erdemcanaz/EE313-Term-project/Pictures/Control Unit/control unit4.png

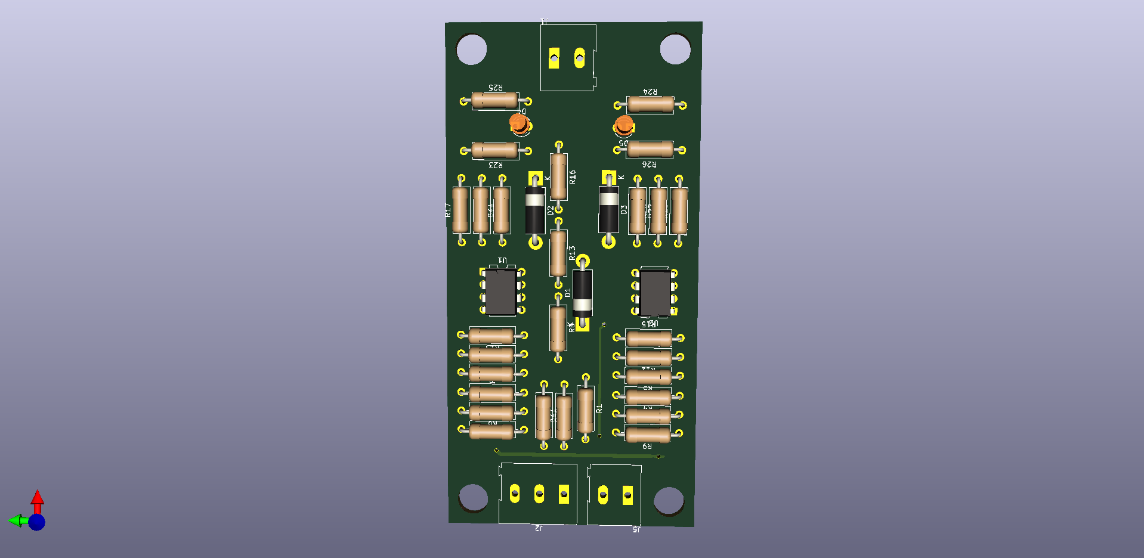
Pictures/Control Unit/control unit4.png
