erdemcanaz/EE313-Term-project/Pictures/Control Unit/ltspice simulation of fan noisy.png

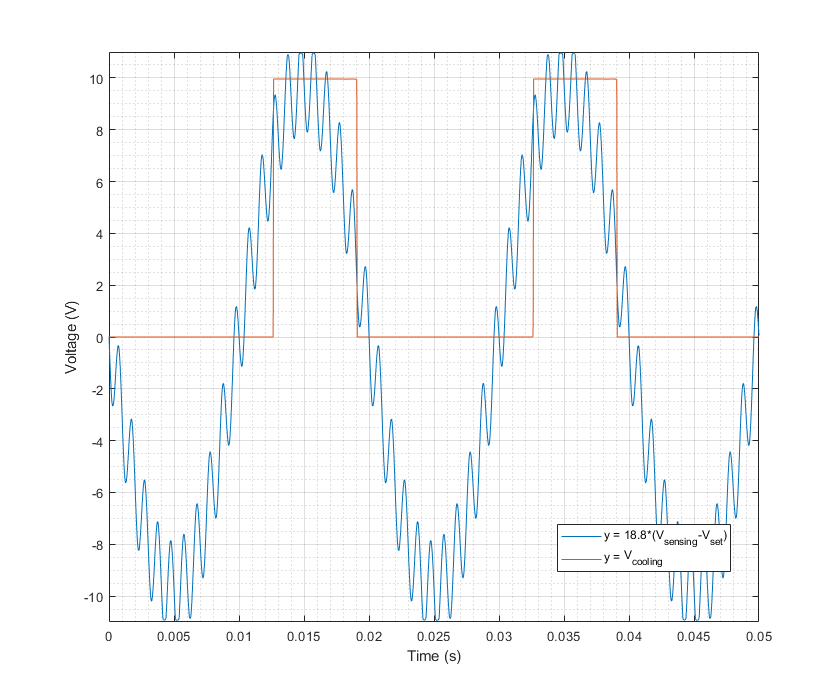
Pictures/Control Unit/ltspice simulation of fan noisy.png
