erdemcanaz/EE313-Term-project/Pictures/Control Unit/ltspice simulation of fan wandwo noise.png

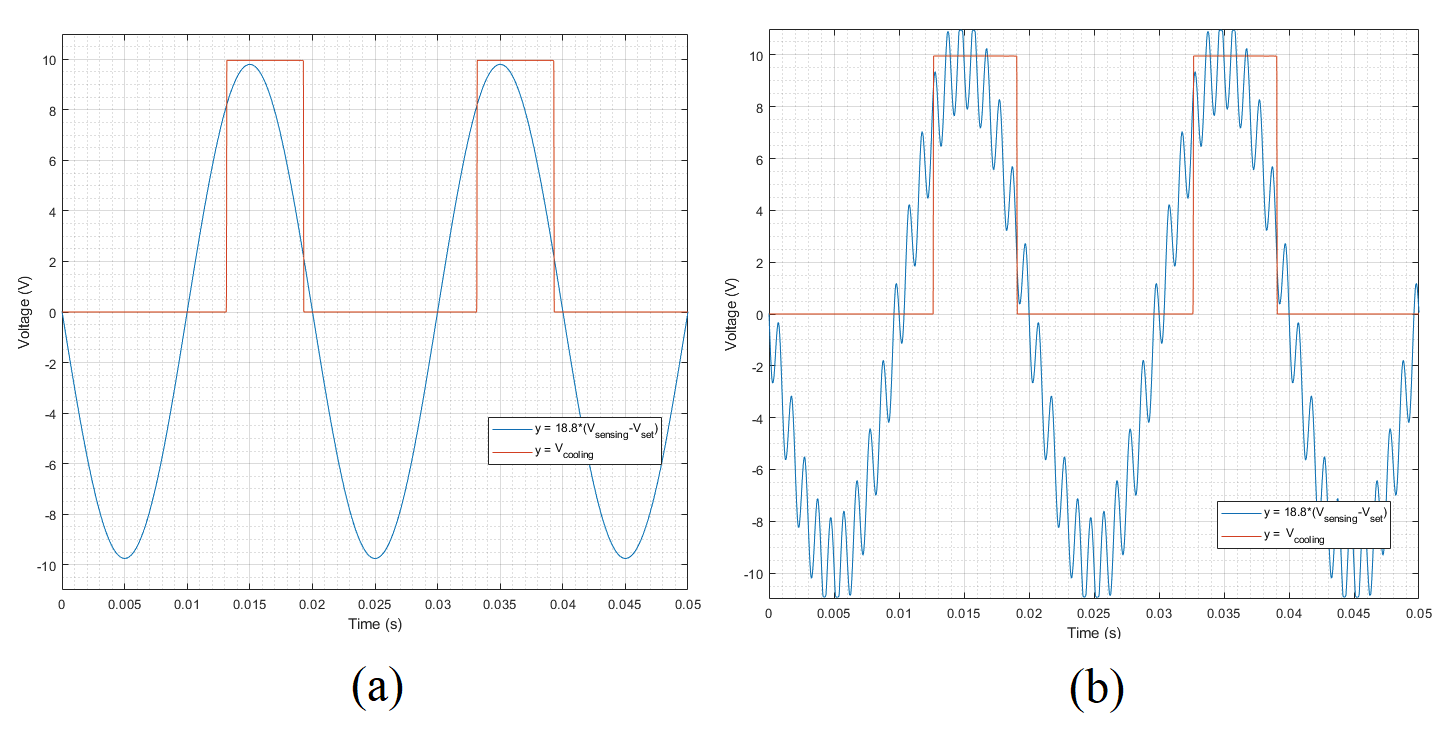
Pictures/Control Unit/ltspice simulation of fan wandwo noise.png
