erdemcanaz/EE313-Term-project/Pictures/Control Unit/ltspice simulation of fan.png

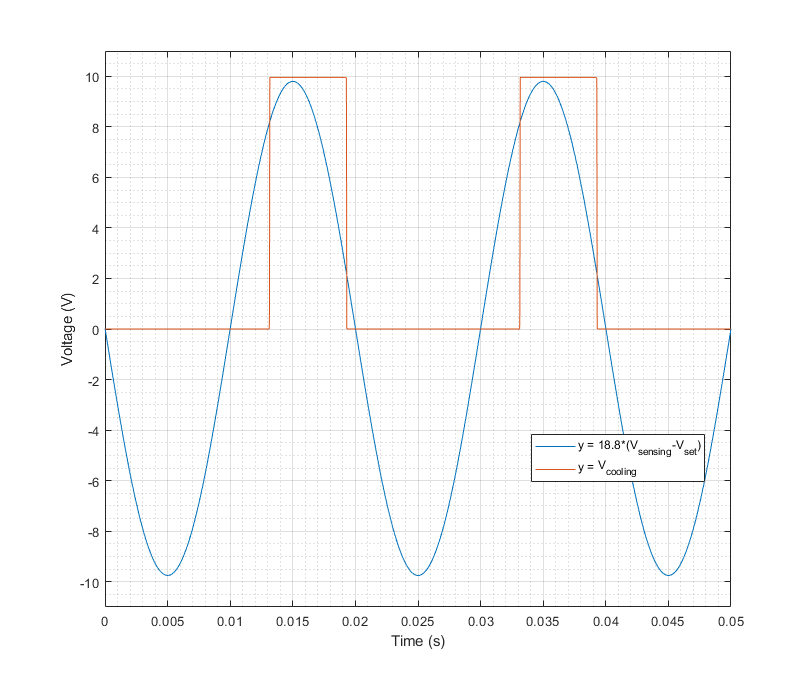
Pictures/Control Unit/ltspice simulation of fan.png
