erdemcanaz/EE313-Term-project/Pictures/Control Unit/schmitt trigger circuit.png

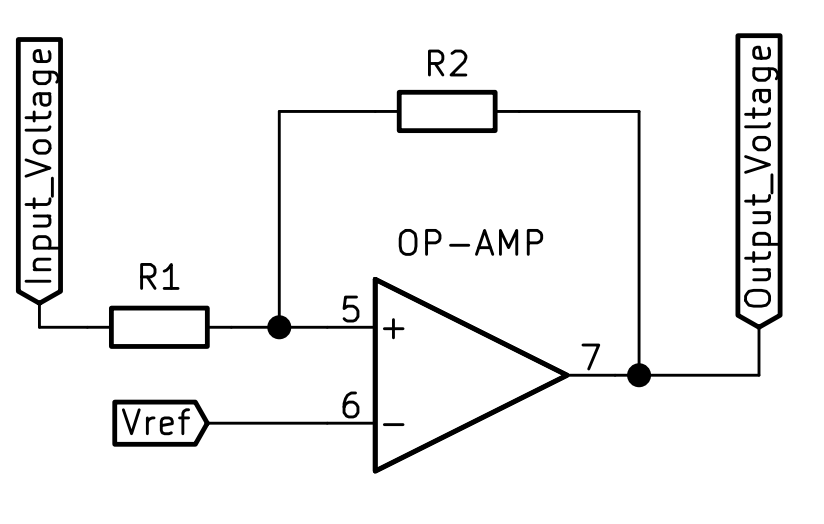
Pictures/Control Unit/schmitt trigger circuit.png
