erdemcanaz/EE313-Term-project/Pictures/display unit/simulationresults.png

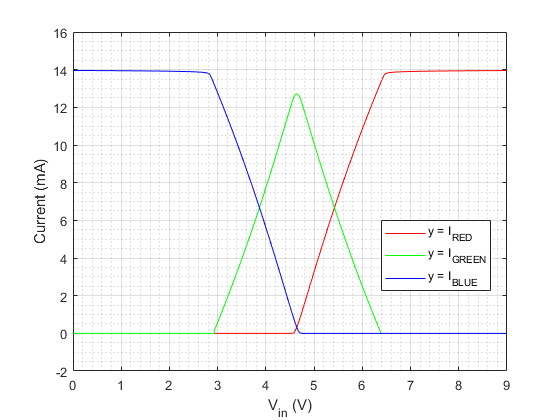
Pictures/display unit/simulationresults.png
