erdemcanaz/EE313-Term-project/Pictures/Sensing Unit/amplified signal.png

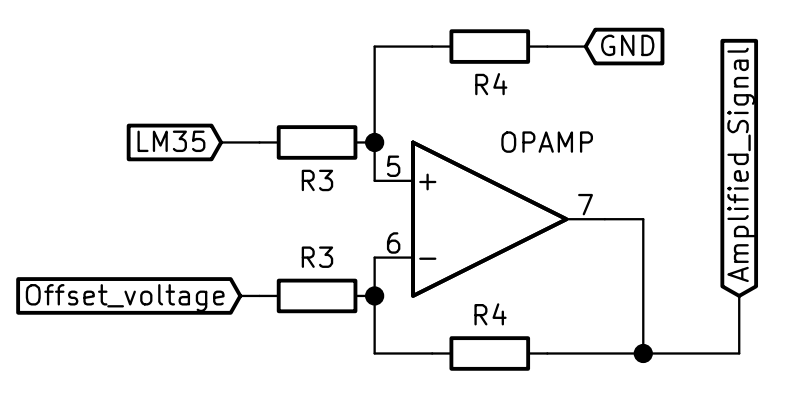
Pictures/Sensing Unit/amplified signal.png
