erdemcanaz/EE313-Term-project/Pictures/Sensing Unit/offset_voltage.png

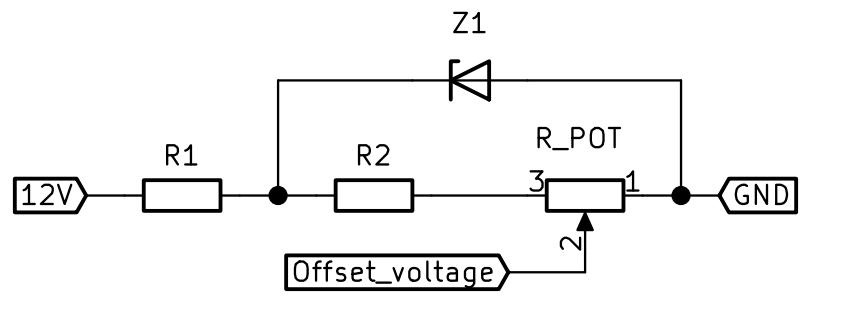
Pictures/Sensing Unit/offset_voltage.png
