erdemcanaz/EE313-Term-project/Pictures/Sensing Unit/osciloscope.png

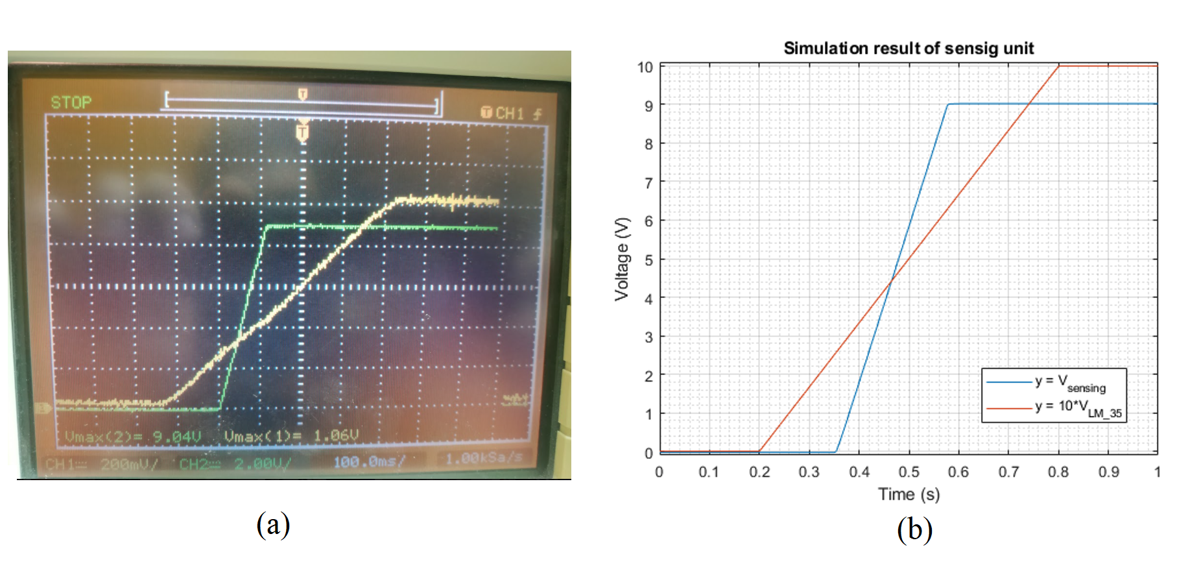
Pictures/Sensing Unit/osciloscope.png
