erdemcanaz/EE313-Term-project/Pictures/Sensing Unit/power connection indicators.png

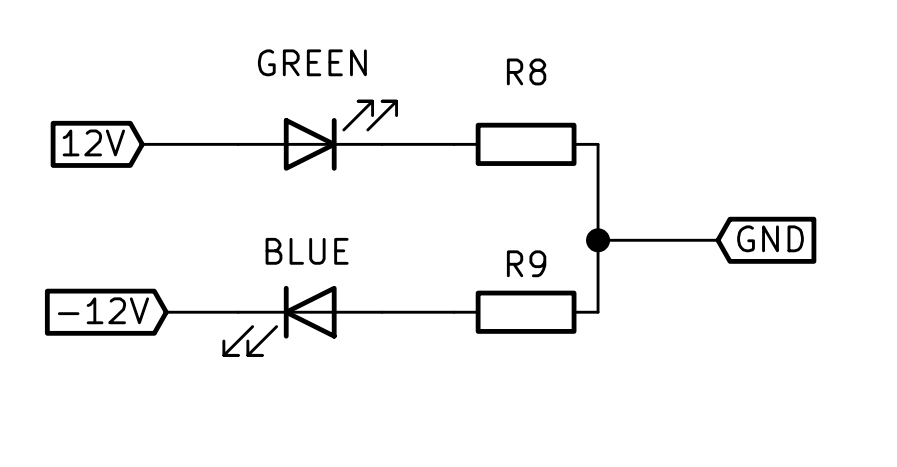
Pictures/Sensing Unit/power connection indicators.png
