erdemcanaz/EE313-Term-project/Simulation/Control Unit - 4/0.2C-0.1mV noise with 1khz on top of 1C temp difference.png

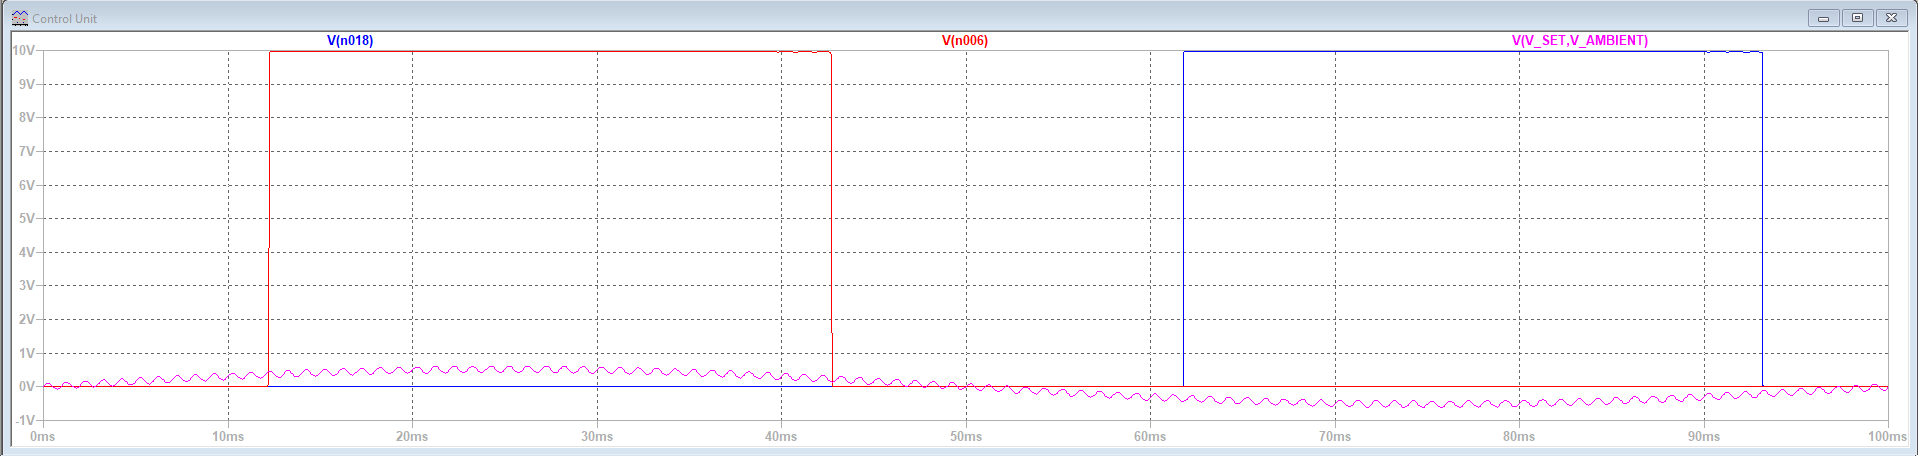
Simulation/Control Unit - 4/0.2C-0.1mV noise with 1khz on top of 1C temp difference.png
