erdemcanaz/EE313-Term-project/Simulation/Control Unit - 4/1C-0.53mV noise with 1khz on top of 1C temperature difference.png

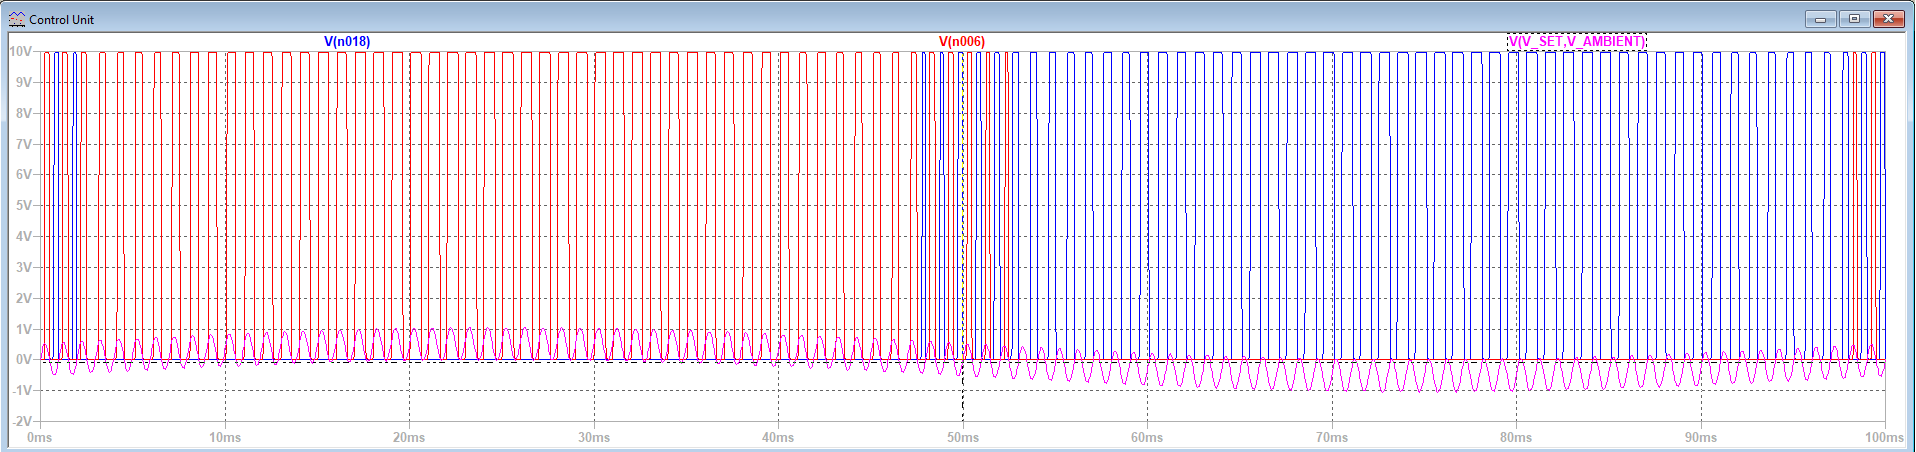
Simulation/Control Unit - 4/1C-0.53mV noise with 1khz on top of 1C temperature difference.png
