erdemcanaz/EE313-Term-project/Simulation/Control Unit - 4/1C-0.53mV noise with 1khz on top of 3C temp difference.png

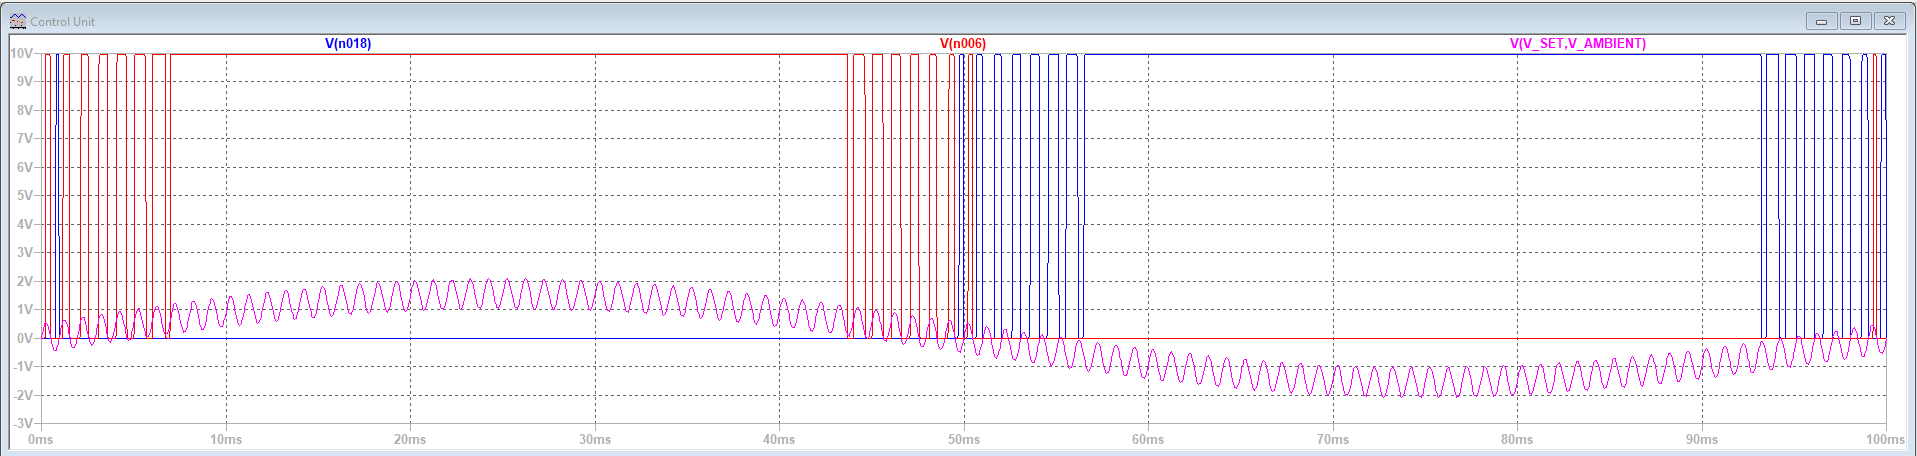
Simulation/Control Unit - 4/1C-0.53mV noise with 1khz on top of 3C temp difference.png
