erdemcanaz/EE313-Term-project/Simulation/Control Unit - 4/fan latching points.png

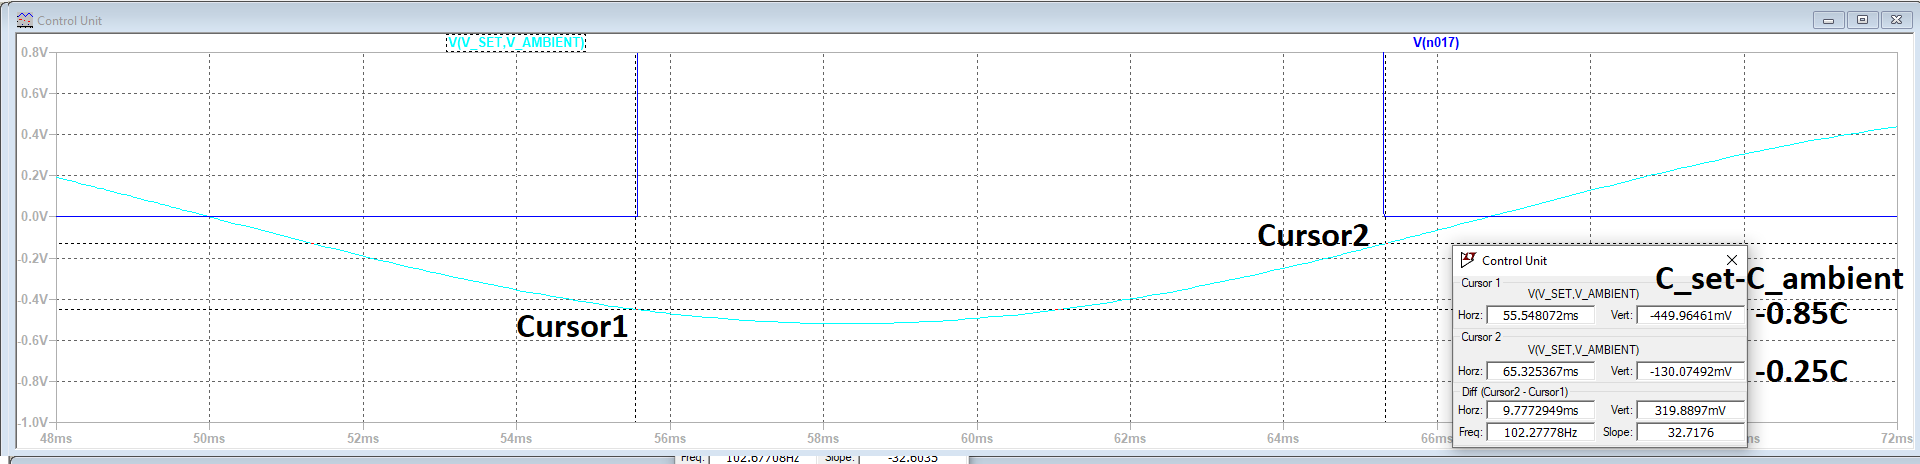
Simulation/Control Unit - 4/fan latching points.png
