erdemcanaz/EE313-Term-project/Simulation/Control Unit - 4/heater latching points.png

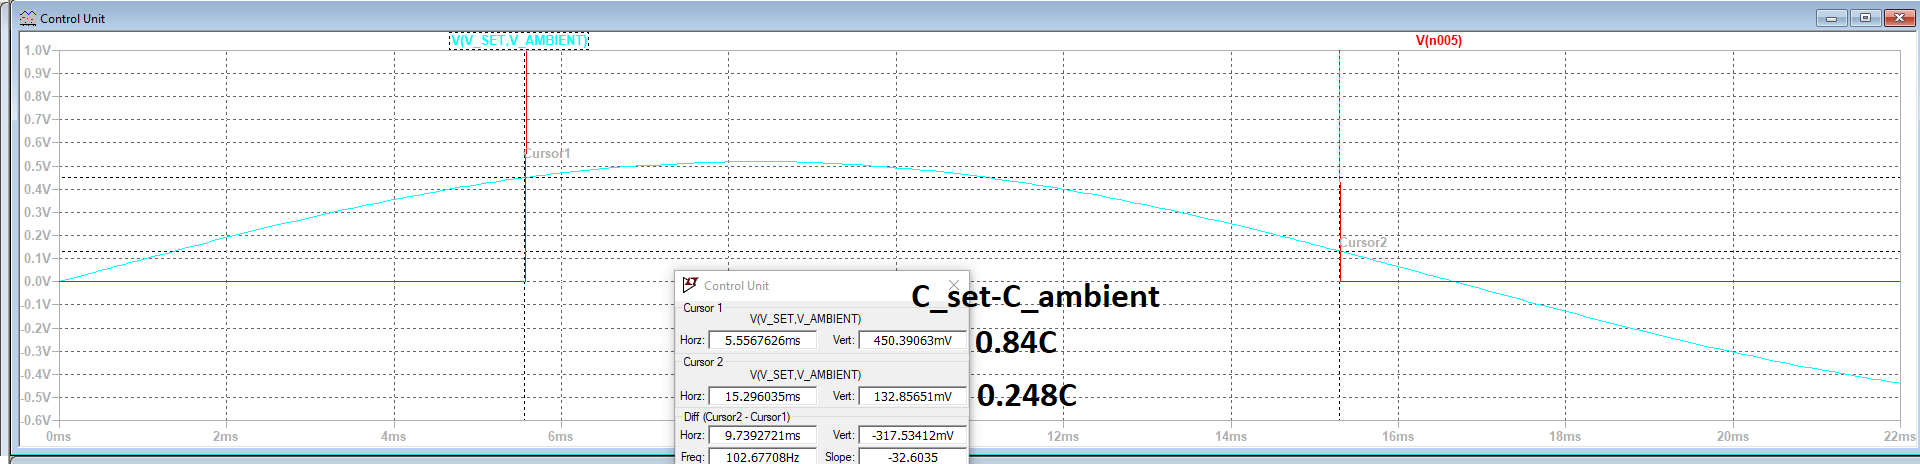
Simulation/Control Unit - 4/heater latching points.png
