erdemcanaz/EE313-Term-project/Simulation/Control Unit - 4/schmit trigger.png

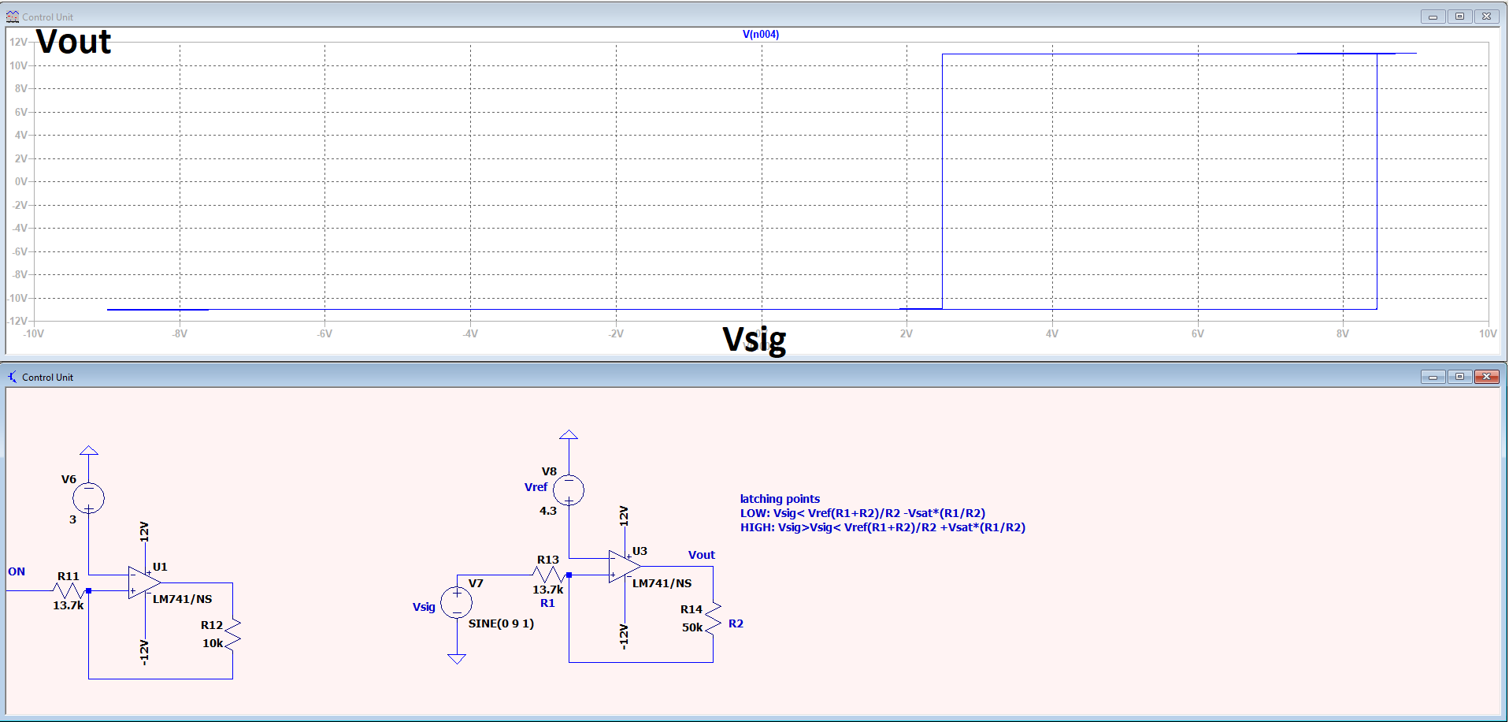
Simulation/Control Unit - 4/schmit trigger.png
