erdemcanaz/EE313-Term-project/Simulation/Control Unit - 4/operation graph with temeprature difference greater than 1C.png

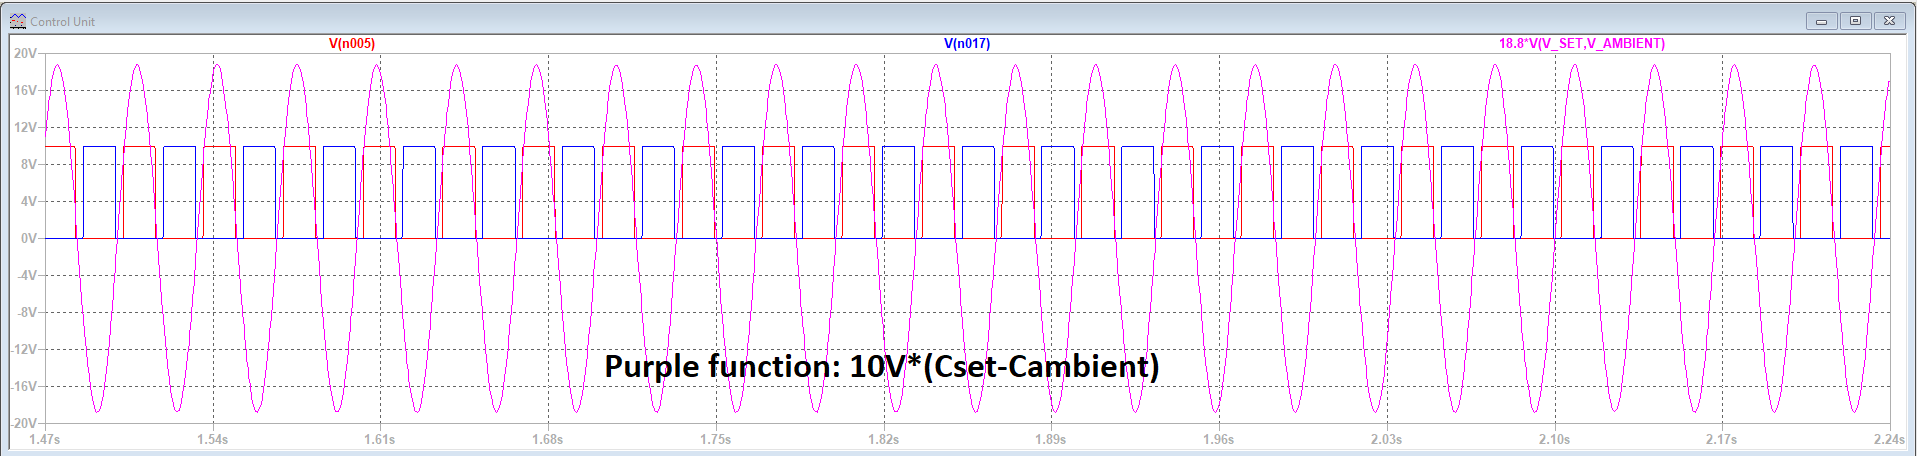
Simulation/Control Unit - 4/operation graph with temeprature difference greater than 1C.png
