erdemcanaz/EE313-Term-project/Simulation/Control Unit - 4/operation graph.png

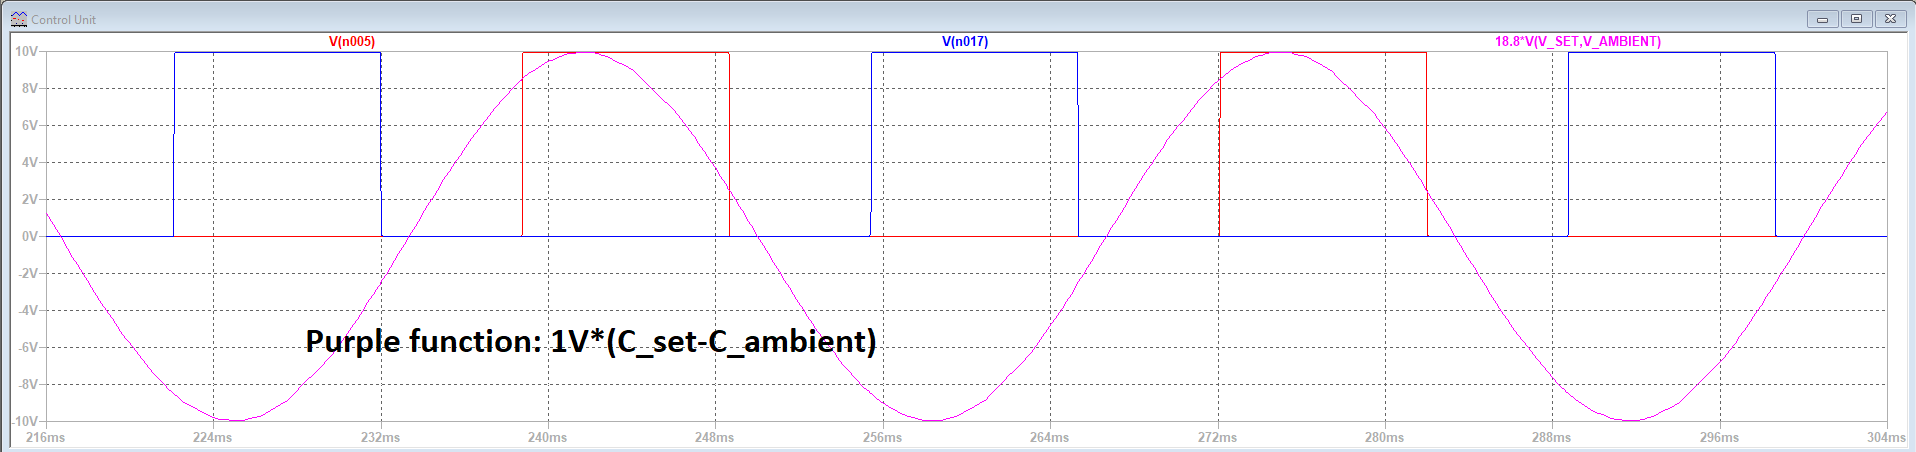
Simulation/Control Unit - 4/operation graph.png
