erdemcanaz/EE313-Term-project/Pictures/Sensing Unit/simulation result1.png

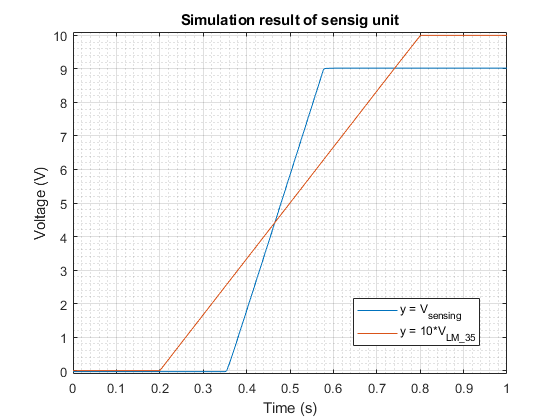
Pictures/Sensing Unit/simulation result1.png
