erdemcanaz/EE313-Term-project/Simulation/Display Unit3/Results.png

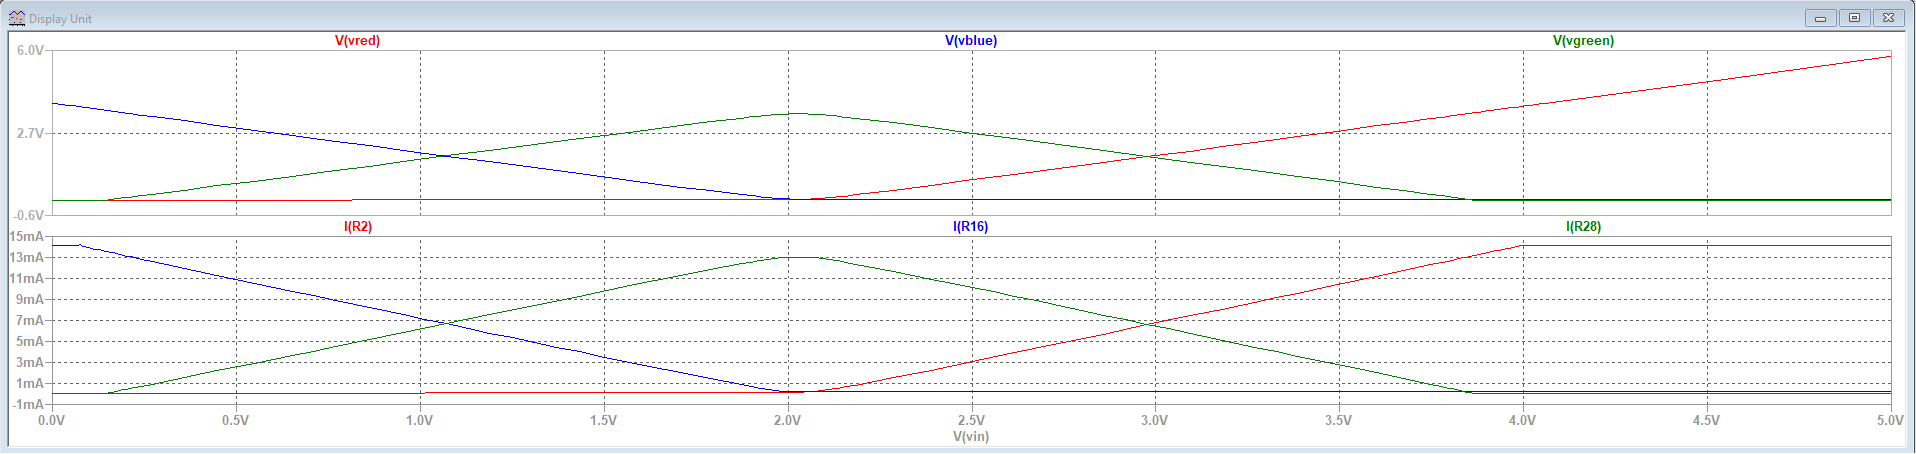
Simulation/Display Unit3/Results.png
