erdemcanaz/EE313-Term-project/Simulation/Sensing Unit.asc

D1: diode
D2: zener; ZD
R1: res; 4500
R2: res; 220
R3: res; 25k
R4: res; 1k
R5: res; 1k
R6: res; 25k
R7: res; 350
R8: res; 10k
U1: opamp2; LM741/NS
U2: opamp2; LM741/NS
U5: opamp2; LM741/NS
V1: voltage; SINE(0.3 0.3 10)
V2: voltage; 12V
V3: voltage; -12V
V4: voltage; 5V
Named nets: 0, LM35, 12V, 5V, -12V, Vout
.include D:\\GITHUB\\EE313-Term-project\\Simulation\\LM741.MOD
.tran 0 1 0
X1
X2
X3
X4
X3
X4
Vd
Vdd
Vout = { [ LM35 - ( (X2/ (X0+X1+X2) )*Vdd )  ]* (X3/X4)  } - Vd,  Vout <V_zenner
LM35: analog voltage output of LM35 temperature sensor
Vdd: Voltage output of 5V linear voltage source
Vd: voltage drop of diode
X0
Vout is zero if Voltage of LM35 is smaller 
than voltage output of this section
Substraction
Note that voltage output of this section is always positive
Voltage Follower
Note that this section limits upper value of
Vout to 4.7V
POTENTIOMETER-500Ohm
SET POTENTIOMETER SUCH THAT WHEN 
LM35 IS 0.24V, Vout STARTS TO INCREASE
.model ZD D(Bv=4.7 type=zener)
