erdemcanaz/EE313-Term-project/Simulation/Display Unit3/Display Unit.asc

D1: LED
D2: LED
D3: diode
D4: diode
D5: zener; TDZ6_8B
D6: LED
D7: zener; TDZ6_8B
Q1: npn
Q2: npn; BC547B
Q3: npn; BC547B
R1: res; 65k
R2: res; 10k
R3: res; 50k
R4: res; 100k
R5: res; 200k
R6: res; 100k
R7: res; 200k
R8: res; 2k
R9: res; 3k
R10: res; 100k
R11: res; 2k
R12: res; 7k
R13: res; 200k
R14: res; 100k
R15: res; 2.2k
R16: res; 700
R17: res; 1.5k
R18: res; 65k
R19: res; 100
R20: res; 700
R21: res; 300
R22: res; 10k
R23: res; 100k
R24: res; 100k
R26: res; 100
R28: res; 800
U2: opamp2; LM741/NS
U3: opamp2; LM741/NS
U6: opamp2; LM741/NS
V1: voltage; PWL(0 0 0.1 9)
V2: voltage; 12V
V3: voltage; -12V
V4: voltage; 5V
Named nets: 0, Vin, 12V, -12V, 5V, Vred, Vblue
.include D:\\GITHUB\\EE313-Term-project\\Simulation\\Display Unit\\LM741.MOD
.tran 0 0.1 0
in the range of 0-9V
Vin(C) = 0.53 *(C-24)
Vin(24C)=0V, Vin(40C)=9V
2*(Vin-Vref_red-Vdiode/2); >0
2*(Vref_blue-Vin-Vdiode/2); >0
Vref_red
RED
GREEN
BLUE
