erdemcanaz/EE313-Term-project/Simulation/Sensing Unit - 2/Sensing Unit.asc

D1: diode
D2: zener; UDZV9_1B
D3: LED
D4: zener; 1N750
R1: res; 3k
R2: res; 2.5k
R3: res; 25k
R4: res; 1k
R5: res; 1k
R6: res; 25k
R7: res; 45k
R8: res; 10k
R9: res; 0
R10: res; 560
R11: res; 500k
U1: opamp2; LM741/NS
U2: opamp2; LM741/NS
U3: opamp2; LM741/NS
U5: opamp2; LM741/NS
V1: voltage; PWL(0 0 0.2 0 0.8 1 1 1)
V2: voltage; 12
V3: voltage; -12V
V4: voltage; 5V
Named nets: 0, LM35, 12V, -12V, 5V, Vout
.include D:\\GITHUB\\EE313-Term-project\\Simulation\\Sensing Unit\\LM741.MOD
.tran 0 1 0
X1
X2
X3
X4
X3
X4
Vd
Vdd
Vout = { [ LM35 - ( (X2/ (X0+X1+X2) )*Vdd )  ]* (X3/X4)  } - Vd,  Vout <V_zenner
LM35: analog voltage output of LM35 temperature sensor
Vdd: Voltage output of 5V linear voltage source
Vd: voltage drop of diode
X0
Vout is zero if Voltage of LM35 is smaller 
than voltage output of this section
Substraction
Note that voltage output of this section is always positive
Voltage Follower
Note that this section limits upper value of
Vout to V_zenner
SET POTENTIOMETER SUCH THAT WHEN 
LM35 IS 0.24V, Vout STARTS TO INCREASE
.model ZD D(Bv=4.7 type=zener)
