erdemcanaz/EE313-Term-project/Simulation/Set unit/Set unit.asc

R1: res; 3k
R2: res; 40k
R_POT2: res; R= 100k-V(R_POT_1)
R_POT_1: res; R=V(R_POT_1)
U3: opamp2; LM741/NS
V1: voltage; PWL(0 0 0.2 0 0.8 1 1 1)
V2: voltage; 12
V3: voltage; -12V
V4: voltage; 5V
V5: voltage; ""
Named nets: 0, LM35, 12V, -12V, 5V, Vset, R_POT_1
.include D:\\GITHUB\\EE313-Term-project\\Simulation\\Sensing Unit\\LM741.MOD
;tran 0 1 0
.dc V5 1 100000
