erdemcanaz/EE313-Term-project/Simulation/Display unit- current mirror/display unit current mirror.asc

D1: LED
D4: LED
D5: LED
Q2: npn; BC547B
Q3: pnp; BC556B
Q4: pnp; BC556B
Q5: npn; BC547B
R1: res; 140k
R2: res; 100
R3: res; 100
R4: res; 650
R5: res; 500
R6: res; 150k
V1: voltage; PWL(0 9 1.1 0 2 0)
V2: voltage; 12V
V3: voltage; PWL(0 0 0.95 0 2 9)
V4: voltage; -12V
Named nets: 0, 12V, B, -12V, R
.tran 0 2 0.01
