erdemcanaz/EE313-Term-project/Simulation/Control Unit - 3/Control Unit.asc

R15: res; 1000k
R16: res; 1000k
R22: res; 10k
R23: res; 3k
U6: opamp2; LM741/NS
V1: voltage; SINE(2 2 1 0 0 180)
V2: voltage; 12V
V3: voltage; -12V
V4: voltage; 5V
V5: voltage; 2
V6: voltage; SINE(0 12 1)
V7: voltage; SINE(0 0 200)
V8: voltage; 3.84
Named nets: 0, V_SET, 12V, -12V, 5V, V_AMBIENT
.include D:\\GITHUB\\EE313-Term-project\\Simulation\\Control Unit\\LM741.MOD
.tran 0 10 0
V(C)=0.25*(C-24); 0<V(C)<4.7
V(24)=0
V(40)=4
0<V_SET<4.5
1C = 0.25V
SCHMITT TRIGGER
