erdemcanaz/EE313-Term-project/KiCad/sensing unit1/sensing unit1.kicad_pcb

## KiCad design KiCad/sensing unit1/sensing unit1.kicad_pcb (2022-01-15)

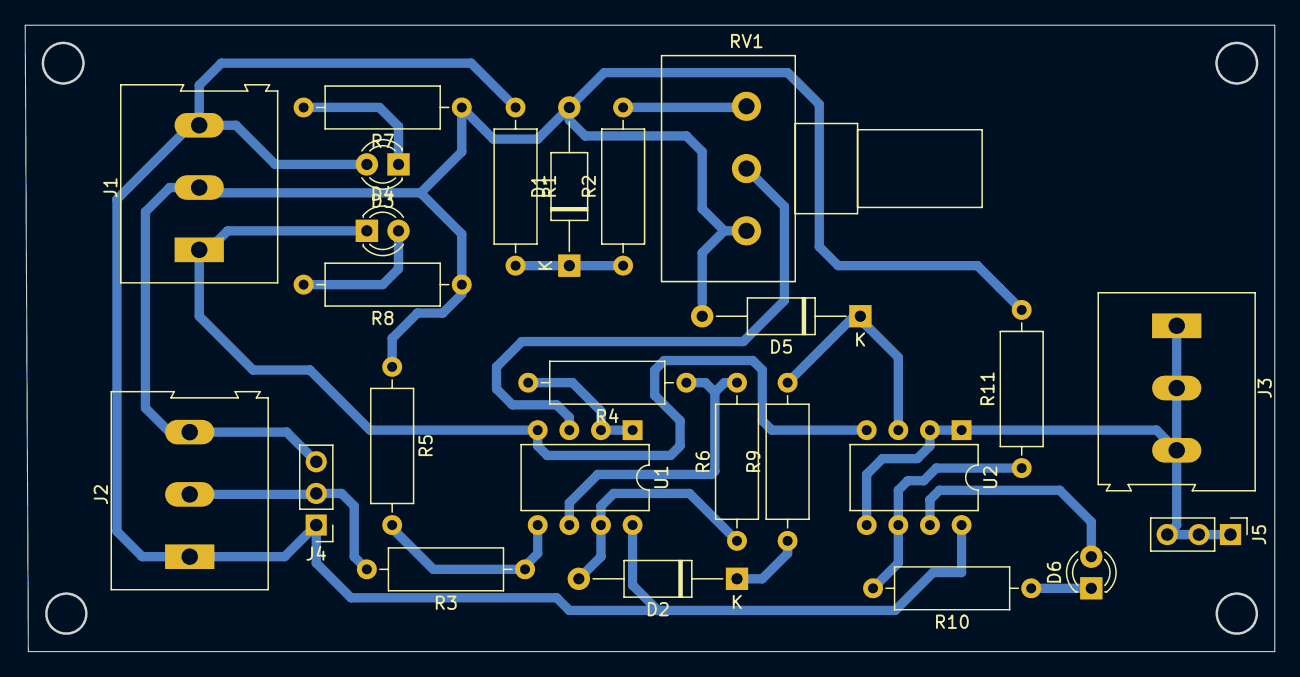
[picture p77: board sensing unit1.kicad_pcb from above]

Board: 2 copper layers, 100.3 x 50.3 mm, 25 parts (0 on the bottom side), 19 nets.

Parts:
D1: 5.1V; D_A-405_P12.70mm_Horizontal
D2: D; D_A-405_P12.70mm_Horizontal
D3: GREEN; LED_D3.0mm_FlatTop
D4: BLUE; LED_D3.0mm_FlatTop
D5: 4.7V; D_A-405_P12.70mm_Horizontal
D6: RED; LED_D3.0mm_FlatTop
J1, J2, J3: Conn_01x03_Male; TerminalBlock_Altech_AK300-3_P5.00mm
J4, J5: Conn_01x03_Male; PinHeader_1x03_P2.54mm_Vertical
R1: 3k; R_Axial_DIN0309_L9.0mm_D3.2mm_P12.70mm_Horizontal
R2: 50k; R_Axial_DIN0309_L9.0mm_D3.2mm_P12.70mm_Horizontal
R3, R4, R10: 1k; R_Axial_DIN0309_L9.0mm_D3.2mm_P12.70mm_Horizontal
R5, R6: 25k; R_Axial_DIN0309_L9.0mm_D3.2mm_P12.70mm_Horizontal
R7, R8: 1.2k; R_Axial_DIN0309_L9.0mm_D3.2mm_P12.70mm_Horizontal
R9: 10k; R_Axial_DIN0309_L9.0mm_D3.2mm_P12.70mm_Horizontal
R11: 330; R_Axial_DIN0309_L9.0mm_D3.2mm_P12.70mm_Horizontal
RV1: 5k; Potentiometer_Alps_RK163_Single_Horizontal
U1, U2: LM358; DIP-8_W7.62mm

Connections:
12V: D3.2, J1.3, J2.1, J4.1, R1.1, U1.8, U2.8
-12V: D4.1, J1.1, U1.4, U2.4
GND: D1.2, D5.2, J1.2, J2.3, J4.3, R5.1, R7.1, R8.1, R11.2, RV1.1
LM35: J2.2, J4.2, R3.2
unnamed: D1.1, R1.2, R2.1
unnamed: D2.1, R9.1
unnamed: D2.2, R6.1, U1.7
unnamed: D3.1, R7.2
unnamed: D4.2, R8.2
unnamed: D5.1, R9.2, U2.3
unnamed: D6.1, R10.1
unnamed: D6.2, U2.7
unnamed: R2.2, RV1.3
unnamed: R3.1, R5.2, U1.5
unnamed: R4.1, R6.2, U1.6
unnamed: R4.2, U1.1, U1.2
unnamed: R10.2, R11.1, U2.6
unnamed: RV1.2, U1.3
Vout: J3.1, J3.2, J3.3, J5.1, J5.2, J5.3, U2.1, U2.2, U2.5
